chiarac99/2DShapeRenderingPantograph/force model/Hapkit_Pantograph_ForceFeedback_motor1_v1_slowOK.ino

//--------------------------------------------------------------------------
// ME327 Team 10 - Pantograph Haptic Shape Renderer
// Penetration depth + Force feedback function
//
// This file implements:
//   (1) A closed-loop shape (default: fat round-cornered star, 180 pts)
//       with a clearly marked slot for swapping in real Python-generated shapes
//   (2) Arc-length precomputation for texture rendering
//   (3) CCW winding check at startup (signed area via shoelace formula)
//   (4) Nearest-segment search + signed distance (penetration depth)
//   (5) Ray-casting inside/outside test
//   (6) Force feedback model with three regions on SIGNED penetration depth
//       (d > 0 = inside, d < 0 = outside):
//         d > 0:          linear wall spring + damping + (optional) texture
//         P_T < d <= 0:   dead zone, F = 0
//         d <= P_T:       exponential guidance pulling toward outline
//   (7) Two modes: MODE_CONTROL (no texture) and MODE_TEXTURED (sinusoidal)
//   (8) Forward kinematics (geometric, with corrected signs)
//   (9) Jacobian transpose (Cartesian force -> motor torques)
//   (10) PWM motor command output with direction control
//
// [TUNE WHEN HARDWARE READY] markers throughout the file flag values
// that need to be confirmed or re-calibrated once the pantograph is
// physically built.
//--------------------------------------------------------------------------

#include <math.h>
#include <avr/pgmspace.h>
#include <SoftwareSerial.h>

// ============================================================
// BOARD ROLE
// ============================================================
// Both Hapkit boards run identical firmware EXCEPT for this single line.
// Comment/uncomment to indicate which motor this board controls:
//
//   #define IS_MOTOR_1   <- this board drives motor 1 (theta_1 = own encoder)
//   (commented out)      <- this board drives motor 5 (theta_5 = own encoder)
//
// Both boards independently compute the full force model and both
// torques (tau1, tau5) via the Jacobian transpose. Each board then
// writes ONLY ITS OWN torque to its local motor:
//   IS_MOTOR_1 defined   -> writes tau1
//   IS_MOTOR_1 undefined -> writes tau5
//
// Hardware communication: the two boards exchange joint angles via a
// SoftwareSerial link on pins D9 (TX) and D10 (RX), keeping the hardware
// UART on D0/D1 free for USB Serial Monitor debugging. No host PC is
// needed in the control loop. Each board sends its own theta as
// "A<value>\n" and receives the partner's theta the same way.
//
// Wiring between boards (in addition to common GND):
//   Board 1 D9 (TX)  ->  Board 2 D10 (RX)
//   Board 1 D10 (RX) <-  Board 2 D9  (TX)
#define IS_MOTOR_1


// ============================================================
// PANTOGRAPH LINK LENGTHS  [meters]
// ============================================================
// Used by forward kinematics and Jacobian (stubs at the bottom of this
// file). Modify here when CAD is finalized. Convention follows Campion
// et al. 2005, with motor pivots coincident (a5 = 0) for wider workspace.
//
// Note: named LINK_A1..LINK_A5 (not A1..A5) because Arduino reserves the
// short A1..A5 names for analog pin aliases (PIN_A1, PIN_A2, ...).
//
//        P3 (pen tip)
//       /  \
//     a3    a2
//     /      \
//    P4      P2
//    |        |
//    a4       a1
//    |        |
//      P5/P1   <-- both motor pivots; a5 = 0 (coincident)
//
// [TUNE WHEN HARDWARE READY: set these to the actual CAD lengths]
const float LINK_A1 = 0.10f;    // proximal link, motor 1 side
const float LINK_A2 = 0.10f;    // distal link, motor 1 side (P2 -> P3)
const float LINK_A3 = 0.10f;    // distal link, motor 5 side (P4 -> P3)
const float LINK_A4 = 0.10f;    // proximal link, motor 5 side
const float LINK_A5 = 0.000f;    // distance between motor pivots (coincident)


// ============================================================
// HAPKIT HARDWARE PIN ASSIGNMENTS
// ============================================================
// From HapkitBoardPinMapping.pdf (v 11.14.2013):
//   D5  Motor 1 PWM
//   D6  Motor 2 PWM (unused in two-board pantograph; used in single-board)
//   D7  Motor 2 direction (unused in two-board)
//   D8  Motor 1 direction
//   D9  Grove connector output (used here as SoftwareSerial TX to partner)
//   D10 Grove connector output (used here as SoftwareSerial RX from partner)
//   A2  MR sensor (this board's encoder)
// [TUNE WHEN HARDWARE READY: if this is the "motor 5" board rather than
//  the "motor 1" board, change neither the pin numbers nor the variable
//  names -- just swap which torque the local motor receives in
//  sendMotorCommand below.]
const int sensorPosPin   = A2;     // MR sensor input
const int PWM_PIN_LOCAL  = 5;      // D5 PWM for this board's motor
const int DIR_PIN_LOCAL  = 8;      // D8 direction for this board's motor

// SoftwareSerial pins for the inter-board UART (D9 TX, D10 RX). The
// hardware UART (D0/D1) is reserved for USB Serial Monitor debugging.
const int LINK_TX_PIN    = 9;      // D9 -> partner's D10
const int LINK_RX_PIN    = 10;     // D10 <- partner's D9
SoftwareSerial linkSerial(LINK_RX_PIN, LINK_TX_PIN);  // (rx, tx)


// ============================================================
// CAPSTAN DRIVE TRANSMISSION  (per Hapkit board)
// ============================================================
// On the Hapkit, the motor pulley rotates the sector pulley via a
// capstan-drive cable, with a transmission ratio set by their radii.
// Tp = F * (r_handle * r_pulley) / r_sector             (A3 Hapkit, scalar)
// For the pantograph, the SAME capstan transmission converts motor torque
// to torque-at-the-proximal-link, but the link rotation directly drives
// the corresponding theta (no separate "handle" variable here; the link
// itself acts as the handle).
//
// Default values are the A3 Hapkit radii. Re-measure for the pantograph
// build if the capstan radii differ (e.g. if you change the drum or use
// a different sector size).
// [TUNE WHEN HARDWARE READY]
const float R_PULLEY  = 0.0045f;    // m, motor capstan/drum radius   (A3: 0.0045)
const float R_SECTOR  = 0.048f;     // m, sector pulley radius         (A3: 0.075)
// R_HANDLE was 0.087 m on the A3 Hapkit but it represents the distance
// from the sector axis to the user's handle. On the pantograph the user
// doesn't grip the sector directly -- they hold the pen tip P3 -- so
// R_HANDLE doesn't apply the same way. The Jacobian transpose already
// maps F at P3 to torque at each motor's sector, so we only need the
// capstan ratio (R_PULLEY / R_SECTOR) here.
//
// Capstan ratio for converting sector torque to motor torque:
//   tau_motor = tau_sector * (R_PULLEY / R_SECTOR)
const float CAPSTAN_RATIO = R_PULLEY / R_SECTOR;


// ============================================================
// TORQUE-TO-PWM CALIBRATION
// ============================================================
// Conversion formula from A3: duty = sqrt(|tau_motor| / TORQUE_TO_DUTY_K)
// The constant 0.0183 was calibrated for the single-Hapkit setup
// (relates motor-pulley torque to PWM duty cycle through the motor's
// torque constant + amplifier gain).
// [TUNE WHEN HARDWARE READY: re-measure for the pantograph motors if
//  they differ from the A3 Hapkit's, e.g. by applying a known voltage
//  and measuring the stall torque.]
const float TORQUE_TO_DUTY_K = 0.0183f;


// ============================================================
// ENCODER CALIBRATION  (from A3)
// ============================================================
// [TUNE WHEN HARDWARE READY: re-measure on each Hapkit board]
const float ENC_M    = -0.0221f;            // deg per encoder count (motor 1, R^2=0.997)
const float ENC_B    = 0.0f;             // deg offset; updatedPos=0 at 0deg by design
const float SECTOR_GEAR_REDUCTION = 1.0f;  // (motor angle) / (sector angle).
                                           // 1.0 if encoder directly measures
                                           // motor pulley; else the gear ratio.



// ============================================================
// CONDITION TOGGLE
// ============================================================
// Switch between control (no texture) and textured rendering.
// Later this can be set by a serial command from Processing so
// the database can log which condition each trial used.
enum RenderMode { MODE_CONTROL = 0, MODE_TEXTURED = 1 };
RenderMode renderMode = MODE_TEXTURED;   // change for testing


// ============================================================
// FORCE MODEL PARAMETERS (placeholders based on A3/A4 values)
// ============================================================
// Sign convention: penetration_depth d is SIGNED.
//   d > 0   -> user is INSIDE the shape (positive = penetrated)
//   d < 0   -> user is OUTSIDE the shape
//   |d|     -> perpendicular distance to the nearest segment of the outline
//
// Three regions on signed d:
//   d > 0:          F = -K_WALL * d        (linear wall, pushes outward)
//                                          (+ texture in textured mode)
//                                          (+ wall damping when moving in)
//   P_T < d <= 0:   F = 0                  (dead zone near the outline)
//   d <= P_T:       F = A_GUIDE * exp(-C_GUIDE * (d - P_T))
//                                          (guidance pulling toward shape;
//                                           peaks at A_GUIDE at d = P_T,
//                                           grows as d gets more negative)

// Inside-shape linear wall stiffness.
const float K_WALL = 2000.0f;       // N/m

// Wall damping (only active when user is moving INTO the wall, v_n > 0).
// Adds B_WALL * v_normal to the wall force. Improves stability (lets us
// run K_WALL higher than the undamped A2 bound would allow) and makes
// impacts feel more solid by dissipating kinetic energy on contact.
const float B_WALL = 15.0f;         // Ns/m

// Dead zone width (P_T is negative -- it's a depth on the outside).
const float P_T = -0.003f;          // m, 3 mm dead zone outside the outline

// Exponential guidance force parameters:
//   A_GUIDE       = force magnitude at d = P_T (peak at zone edge)
//   C_GUIDE       = decay rate (1/m); larger = sharper drop-off near P_T
//   F_GUIDE_MAX   = saturation ceiling for guidance force; once the exp
//                   exceeds this value, F is clamped to F_GUIDE_MAX
//                   so the motors never command more than they can deliver
const float A_GUIDE     = 0.5f;     // N, peak guidance force at d = P_T
const float C_GUIDE     = 200.0f;   // 1/m; exp doubles every ~3.5 mm further out
const float F_GUIDE_MAX = 2.0f;     // N, clamp ceiling (set to ~motor force limit)

// Texture parameters (for MODE_TEXTURED):
const float A_TEX = 0.30f;          // N, texture amplitude
const float LAMBDA_TEX = 0.0020f;   // m, spatial wavelength (2 mm bumps)


// ============================================================
// SHAPE DATA
// ============================================================
// Three closed-loop shapes derived from SVG outlines by the Python
// preprocessing script (preprocess_shapes.py). Each is 200 points,
// normalized so it fits in a ~7 cm bounding box centered at the
// origin, CCW winding. Coordinates are in meters.
//
// Switch between them at runtime by changing CURRENT_SHAPE, or by
// sending a single ASCII character over Serial: 'B' (bunny),
// 'H' (hammer), 'P' (pear).  Later this command will come from
// Processing when the user clicks "Next shape" in the UI.
//
// NOTE: Each shape array currently ends with a duplicate of the first
// point (a relic of the Python script's "close the curve" step). The
// findNearestSegment loop guards against the resulting zero-length
// segment, but consider trimming the duplicate (and dropping N to 199)
// in the next Python regen for cleanliness.

enum ShapeId { SHAPE_BUNNY = 0, SHAPE_HAMMER = 1, SHAPE_PEAR = 2 };
ShapeId currentShape = SHAPE_BUNNY;     // change here for testing

// All shapes happen to have the same point count for now (200), but the
// architecture allows different counts per shape if needed.
const int N_BUNNY  = 200;
const int N_HAMMER = 200;
const int N_PEAR   = 200;

// ----- bunny, 200 pts, CCW -----
const float shape_bunny[N_BUNNY][2] PROGMEM = {
    {  0.00328f,  0.03500f},
    {  0.00198f,  0.03445f},
    {  0.00007f,  0.03328f},
    { -0.00150f,  0.03201f},
    { -0.00281f,  0.03115f},
    { -0.00705f,  0.02830f},
    { -0.00908f,  0.02652f},
    { -0.01059f,  0.02515f},
    { -0.01081f,  0.02493f},
    { -0.01092f,  0.02487f},
    { -0.01101f,  0.02487f},
    { -0.01108f,  0.02487f},
    { -0.01114f,  0.02487f},
    { -0.01118f,  0.02489f},
    { -0.01122f,  0.02492f},
    { -0.01125f,  0.02496f},
    { -0.01129f,  0.02500f},
    { -0.01129f,  0.02504f},
    { -0.01123f,  0.02511f},
    { -0.01117f,  0.02531f},
    { -0.01087f,  0.02665f},
    { -0.01087f,  0.02781f},
    { -0.01117f,  0.02907f},
    { -0.01147f,  0.02955f},
    { -0.01210f,  0.03042f},
    { -0.01247f,  0.03064f},
    { -0.01395f,  0.03108f},
    { -0.01449f,  0.03113f},
    { -0.01558f,  0.03088f},
    { -0.01671f,  0.03036f},
    { -0.01714f,  0.02992f},
    { -0.01752f,  0.02924f},
    { -0.01847f,  0.02674f},
    { -0.01906f,  0.02462f},
    { -0.01966f,  0.02211f},
    { -0.01993f,  0.02162f},
    { -0.02006f,  0.02134f},
    { -0.02022f,  0.02119f},
    { -0.02046f,  0.02115f},
    { -0.02206f,  0.02115f},
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
};

// ----- hammer, 200 pts, CCW -----
const float shape_hammer[N_HAMMER][2] PROGMEM = {
    {  0.01861f, -0.01738f},
    {  0.01862f, -0.01740f},
    {  0.01863f, -0.01742f},
    {  0.01864f, -0.01745f},
    {  0.01867f, -0.01748f},
    {  0.01872f, -0.01751f},
    {  0.01886f, -0.01753f},
    {  0.02000f, -0.01752f},
    {  0.02049f, -0.01751f},
    {  0.02071f, -0.01746f},
    {  0.02116f, -0.01727f},
    {  0.02369f, -0.01616f},
    {  0.02512f, -0.01528f},
    {  0.02673f, -0.01401f},
    {  0.02831f, -0.01247f},
    {  0.02961f, -0.01089f},
    {  0.03057f, -0.00940f},
    {  0.03150f, -0.00754f},
    {  0.03217f, -0.00571f},
    {  0.03275f, -0.00326f},
    {  0.03315f, -0.00047f},
    {  0.03318f,  0.00067f},
    {  0.03312f,  0.00140f},
    {  0.03299f,  0.00199f},
    {  0.03278f,  0.00258f},
    {  0.03240f,  0.00334f},
    {  0.03171f,  0.00460f},
    {  0.03157f,  0.00493f},
    {  0.03152f,  0.00513f},
    {  0.03149f,  0.00551f},
    {  0.03150f,  0.00668f},
    {  0.03154f,  0.00701f},
    {  0.03162f,  0.00728f},
    {  0.03179f,  0.00768f},
    {  0.03194f,  0.00797f},
    {  0.03211f,  0.00820f},
    {  0.03234f,  0.00844f},
    {  0.03276f,  0.00878f},
    {  0.03384f,  0.00949f},
    {  0.03401f,  0.00964f},
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
};

// ----- pear, 200 pts, CCW -----
const float shape_pear[N_PEAR][2] PROGMEM = {
    { -0.00260f,  0.03430f},
    { -0.00341f,  0.03469f},
    { -0.00377f,  0.03482f},
    { -0.00411f,  0.03490f},
    { -0.00453f,  0.03496f},
    { -0.00528f,  0.03500f},
    { -0.01129f,  0.03475f},
    { -0.01401f,  0.03468f},
    { -0.01441f,  0.03464f},
    { -0.01462f,  0.03460f},
    { -0.01476f,  0.03455f},
    { -0.01485f,  0.03451f},
    { -0.01493f,  0.03448f},
    { -0.01499f,  0.03444f},
    { -0.01503f,  0.03440f},
    { -0.01507f,  0.03436f},
    { -0.01511f,  0.03432f},
    { -0.01514f,  0.03428f},
    { -0.01516f,  0.03423f},
    { -0.01519f,  0.03418f},
    { -0.01521f,  0.03412f},
    { -0.01522f,  0.03405f},
    { -0.01523f,  0.03397f},
    { -0.01523f,  0.03387f},
    { -0.01522f,  0.03373f},
    { -0.01519f,  0.03353f},
    { -0.01510f,  0.03319f},
    { -0.01481f,  0.03243f},
    { -0.01305f,  0.02866f},
    { -0.01240f,  0.02751f},
    { -0.01193f,  0.02685f},
    { -0.01127f,  0.02609f},
    { -0.01059f,  0.02542f},
    { -0.00997f,  0.02492f},
    { -0.00935f,  0.02450f},
    { -0.00871f,  0.02416f},
    { -0.00807f,  0.02389f},
    { -0.00744f,  0.02369f},
    { -0.00680f,  0.02355f},
    { -0.00617f,  0.02348f},
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
};

// Active shape: a pointer to the current PROGMEM array + its length.
// Shape data lives in flash (PROGMEM) to fit on the ATmega328's small
// RAM (only 2 KB; all three shapes together would be ~4.8 KB if in RAM).
// Access via shapeX(i) / shapeY(i) helpers below, NOT through direct
// indexing -- AVR flash and RAM are on separate buses.
const float (*shape)[2] = shape_bunny;
int N_POINTS = N_BUNNY;

// Read x or y of the i-th vertex of the active shape, from PROGMEM.
inline float shapeX(int i) {
  return pgm_read_float(&shape[i][0]);
}
inline float shapeY(int i) {
  return pgm_read_float(&shape[i][1]);
}



// ============================================================
// PRECOMPUTED TABLES
// ============================================================
// s_arc is sized to the maximum possible point count across all shapes,
// since the active shape can be swapped at runtime. The currently-active
// portion is the first N_POINTS entries.
#define MAX_POINTS 200
float s_arc[MAX_POINTS];
float perimeter = 0.0f;
float lambda_actual = LAMBDA_TEX;


// ============================================================
// VELOCITY TRACKING  (for wall damping)
// ============================================================
// Position from the previous loop, used to compute filtered velocity.
// Same finite-difference + IIR filter pattern as A3/A4.
float xh_prev = 0.0f, yh_prev = 0.0f;
float vx_filt = 0.0f, vy_filt = 0.0f;
const float DT_LOOP = 0.001f;       // s, nominal loop period (1 kHz)


// ============================================================
// ENCODER STATE  (mirrors A3 template)
// ============================================================
// Declared up here (above loop) so the telemetry print can reference
// updatedPos directly without needing extern forward declarations.
int rawPos = 0, lastRawPos = 0, lastLastRawPos = 0;
int rawDiff = 0, lastRawDiff = 0, rawOffset = 0, lastRawOffset = 0;
int flipNumber = 0;
int tempOffset = 0;
bool flipped = false;
const int flipThresh = 700;
int updatedPos = 0;

// Partner-board angle, received over serial.
// [TUNE WHEN HARDWARE READY: pick a sensible startup angle inside the
//  valid workspace, e.g. PI/2 for the elbow-up configuration.]
float theta_partner_rad = PI / 2.0f;

// Last computed pen-tip position (persists between loops when getPenTip
// has bad/no data this iteration).
float xh_persist = 0.0f, yh_persist = 0.0f;


// ============================================================
// FORWARD DECLARATIONS
// ============================================================
void   getPenTipPosition(float &x, float &y, float theta_self);
int    findNearestSegment(float x, float y, float &dist, float &nx, float &ny,
                          float &t_frac);
bool   isInsidePolygon(float x, float y);
void   computeForce(float x, float y, float &Fx, float &Fy);
void   computeMotorTorques(float Fx, float Fy, float &tau1, float &tau5, float theta_self);
void   sendMotorCommand(float tau1, float tau5, float theta_self);
void   precomputeArcLength();
float  signedPolygonArea();
void   checkWinding();
void   setShape(ShapeId s);
void   handleSerialCommands();


// ============================================================
// SETUP
// ============================================================
// PWM frequency divisor helper (copied from A3 template -- DO NOT EDIT).
// Increases PWM frequency on the motor pins to keep motor noise inaudible
// and force-response smooth.
void setPwmFrequency(int pin, int divisor) {
  byte mode;
  if(pin == 5 || pin == 6 || pin == 9 || pin == 10) {
    switch(divisor) {
      case 1: mode = 0x01; break;
      case 8: mode = 0x02; break;
      case 64: mode = 0x03; break;
      case 256: mode = 0x04; break;
      case 1024: mode = 0x05; break;
      default: return;
    }
    if(pin == 5 || pin == 6) {
      TCCR0B = TCCR0B & 0b11111000 | mode;
    } else {
      TCCR1B = TCCR1B & 0b11111000 | mode;
    }
  } else if(pin == 3 || pin == 11) {
    switch(divisor) {
      case 1: mode = 0x01; break;
      case 8: mode = 0x02; break;
      case 32: mode = 0x03; break;
      case 64: mode = 0x04; break;
      case 128: mode = 0x05; break;
      case 256: mode = 0x06; break;
      case 1024: mode = 0x07; break;
      default: return;
    }
    TCCR2B = TCCR2B & 0b11111000 | mode;
  }
}

void setup() {
  Serial.begin(115200);      // USB serial for debugging + user commands
  linkSerial.begin(19200);   // SoftwareSerial inter-board link (D9/D10)
                             // 19200 is the highest baud SoftwareSerial
                             // handles reliably on a 16 MHz AVR.
  linkSerial.setTimeout(10); // cap parseFloat blocking at 10 ms

  // Configure motor PWM at high frequency (matches A3 template).
  setPwmFrequency(PWM_PIN_LOCAL, 1);

  // Configure motor and encoder pins.
  pinMode(sensorPosPin, INPUT);
  pinMode(PWM_PIN_LOCAL, OUTPUT);
  pinMode(DIR_PIN_LOCAL, OUTPUT);
  analogWrite(PWM_PIN_LOCAL, 0);          // motor off at startup
  digitalWrite(DIR_PIN_LOCAL, LOW);

  setShape(currentShape);  // initializes shape pointer, arc-length table, prints CCW check
}


// ============================================================
// MAIN LOOP
// ============================================================
void loop() {
  handleSerialCommands();

  // Sample encoder ONCE per loop. Pass cached value to all functions that
  // need it (rather than re-reading inside each function), since re-reads
  // were confusing the flip-detector during fast motion.
  float theta_self_cached = readThisBoardTheta();

  float xh, yh;
  getPenTipPosition(xh, yh, theta_self_cached);

  float vx = (xh - xh_prev) / DT_LOOP;
  float vy = (yh - yh_prev) / DT_LOOP;
  vx_filt = 0.9f * vx + 0.1f * vx_filt;
  vy_filt = 0.9f * vy + 0.1f * vy_filt;
  xh_prev = xh;
  yh_prev = yh;

  float Fx, Fy;
  computeForce(xh, yh, Fx, Fy);

  // ---- SAFETY: force motors OFF for calibration test ----
  Fx = 0.0f;
  Fy = 0.0f;

  float tau1, tau5;
  computeMotorTorques(Fx, Fy, tau1, tau5, theta_self_cached);

  sendMotorCommand(tau1, tau5, theta_self_cached);

  // Telemetry: print updatedPos every 50 loops so you can watch it sweep
  static int printCounter = 0;
  if (++printCounter >= 50) {
    float ts_deg = ENC_M * updatedPos + ENC_B;
    Serial.print("updatedPos=");  Serial.print(updatedPos);
    Serial.print("  theta_deg=");  Serial.print(ts_deg, 1);
    Serial.print("  partner_rad=");  Serial.print(theta_partner_rad, 3);
    Serial.print("  xh,yh=");     Serial.print(xh, 4);
    Serial.print(",");            Serial.print(yh, 4);
    Serial.println();
    printCounter = 0;
  }
}


// ============================================================
// ENCODER READING + FORWARD KINEMATICS
// ============================================================
// This board reads ONE encoder (its own motor's MR sensor on pin A2) and
// computes θ for that joint. The OTHER joint angle (θ for the other motor)
// must arrive over serial from the partner Hapkit board, or via a host
// (Processing) that polls both boards.
//
// Below, theta1_rad is the angle this board's motor; theta5_rad is the
// other board's motor (received over serial). If this is the "motor 5"
// board, swap the assignments in computeFwdKin() accordingly.
//
// Forward kinematics follows the geometric approach from the wiki:
//   1. P2 = (LINK_A1*cos(theta1), LINK_A1*sin(theta1))
//   2. P4 = (-LINK_A5 + LINK_A4*cos(theta5), LINK_A4*sin(theta5))
//   3. |P2-Pn| = (LINK_A2^2 - LINK_A3^2 + |P4-P2|^2) / (2|P4-P2|)
//   4. Ph = P2 + |P2-Pn|/|P2-P4| * (P4-P2)
//   5. |P3-Ph| = sqrt(LINK_A2^2 - |P2-Pn|^2)
//   6. P3 = Ph + |P3-Ph|/|P4-P2| * (y4-y2, -(x4-x2))    [elbow-up sign]

// --------- Read this board's encoder (returns theta in radians) ---------
// NOTE: this is called multiple times per loop (in getPenTipPosition,
// computeMotorTorques, and sendMotorCommand's theta broadcast). The flip
// state machine assumes consecutive calls correspond to consecutive
// physical timesteps; if you observe flip-counting issues, refactor to
// sample once per loop and cache the result.
float readThisBoardTheta() {
  rawPos = analogRead(sensorPosPin);
  rawDiff = rawPos - lastRawPos;
  lastRawDiff = rawPos - lastLastRawPos;
  rawOffset = abs(rawDiff);
  lastRawOffset = abs(lastRawDiff);
  lastLastRawPos = lastRawPos;
  lastRawPos = rawPos;

  if ((lastRawOffset > flipThresh) && (!flipped)) {
    if (lastRawDiff > 0) flipNumber--; else flipNumber++;
    if (rawOffset > flipThresh) {
      updatedPos = rawPos + flipNumber * rawOffset;
      tempOffset = rawOffset;
    } else {
      updatedPos = rawPos + flipNumber * lastRawOffset;
      tempOffset = lastRawOffset;
    }
    flipped = true;
  } else {
    updatedPos = rawPos + flipNumber * tempOffset;
    flipped = false;
  }

  float ts_deg = ENC_M * updatedPos + ENC_B;            // sector angle (deg)
  float theta_motor_deg = ts_deg * SECTOR_GEAR_REDUCTION;
  float theta_motor_rad = theta_motor_deg * (PI / 180.0f);
  return theta_motor_rad;
}

// --------- Geometric forward kinematics ---------
// Returns true if a valid configuration was found, false otherwise (e.g.
// linkage is in a singular pose).
bool computeFwdKin(float theta1, float theta5, float &x3, float &y3) {
  static int dbg = 0;
  bool doPrint = (++dbg >= 500);
  if (doPrint) dbg = 0;
  
  float x2 = LINK_A1 * cosf(theta1);
  float y2 = LINK_A1 * sinf(theta1);
  float x4 = -LINK_A5 + LINK_A4 * cosf(theta5);
  float y4 = LINK_A4 * sinf(theta5);

  float dx = x4 - x2;
  float dy = y4 - y2;
  float dP2P4 = sqrtf(dx*dx + dy*dy);
  
  if (doPrint) {
    Serial.print("  FK: t1=");Serial.print(theta1,3);
    Serial.print(" t5=");Serial.print(theta5,3);
    Serial.print(" P2=("); Serial.print(x2,3); Serial.print(",");Serial.print(y2,3);
    Serial.print(") P4=("); Serial.print(x4,3); Serial.print(",");Serial.print(y4,3);
    Serial.print(") dP2P4="); Serial.print(dP2P4,4);
    Serial.println();
  }
  
  if (dP2P4 < 1e-6f) { if(doPrint) Serial.println("  -> ret false (singular)"); return false; }

  float dP2Ph = (LINK_A2*LINK_A2 - LINK_A3*LINK_A3 + dP2P4*dP2P4) / (2.0f * dP2P4);
  float h2 = LINK_A2*LINK_A2 - dP2Ph*dP2Ph;
  
  if (doPrint) {
    Serial.print("  dP2Ph="); Serial.print(dP2Ph,4);
    Serial.print(" h2="); Serial.print(h2,6);
    Serial.println();
  }
  
  if (h2 < 0.0f) { if(doPrint) Serial.println("  -> ret false (h2 negative)"); return false; }
  float dP3Ph = sqrtf(h2);

  float xh_pt = x2 + (dP2Ph / dP2P4) * dx;
  float yh_pt = y2 + (dP2Ph / dP2P4) * dy;

  x3 = xh_pt + (dP3Ph / dP2P4) * dy;
  y3 = yh_pt - (dP3Ph / dP2P4) * dx;
  
  if (doPrint) {
    Serial.print("  Ph=("); Serial.print(xh_pt,3); Serial.print(",");Serial.print(yh_pt,3);
    Serial.print(") P3=("); Serial.print(x3,3); Serial.print(",");Serial.print(y3,3);
    Serial.println(") -> ret true");
  }
  return true;
}

// --------- Public function the main loop calls ---------
void getPenTipPosition(float &x, float &y, float theta_self) {
  // theta_self is passed in (cached from loop()) instead of re-reading
  // the encoder, which was triggering spurious flip counts during fast motion.

  // Assign theta1 and theta5 based on which board this is.
#ifdef IS_MOTOR_1
  float theta1 = theta_self;
  float theta5 = theta_partner_rad;
#else
  float theta1 = theta_partner_rad;
  float theta5 = theta_self;
#endif

  float x3, y3;
  if (computeFwdKin(theta1, theta5, x3, y3)) {
    xh_persist = x3;
    yh_persist = y3;
  }
  // If computeFwdKin failed (singular/unreachable), reuse last good value.
  x = xh_persist;
  y = yh_persist;
}


// ============================================================
// PRECOMPUTE ARC-LENGTH TABLE
// ============================================================
// Walks the (closed) shape once to fill s_arc[i] and total perimeter.
// Snaps lambda_actual to perimeter/round(perimeter/LAMBDA_TEX) so the
// sine wave closes cleanly at the seam where shape[N-1] -> shape[0].
void precomputeArcLength() {
  s_arc[0] = 0.0f;
  for (int i = 1; i < N_POINTS; i++) {
    float dx = shapeX(i) - shapeX(i-1);
    float dy = shapeY(i) - shapeY(i-1);
    s_arc[i] = s_arc[i-1] + sqrtf(dx*dx + dy*dy);
  }
  float dx_close = shapeX(0) - shapeX(N_POINTS-1);
  float dy_close = shapeY(0) - shapeY(N_POINTS-1);
  perimeter = s_arc[N_POINTS-1] + sqrtf(dx_close*dx_close + dy_close*dy_close);

  int n_cycles = (int)roundf(perimeter / LAMBDA_TEX);
  if (n_cycles < 1) n_cycles = 1;
  lambda_actual = perimeter / (float)n_cycles;
}


// ============================================================
// SIGNED POLYGON AREA  (shoelace formula)
// ============================================================
// Positive area means CCW winding (interior on the left as you walk
// the array forward). Negative means CW. Used to verify the shape
// array has the orientation the rest of the code assumes.
float signedPolygonArea() {
  float area = 0.0f;
  for (int i = 0; i < N_POINTS; i++) {
    int j = (i + 1) % N_POINTS;
    area += shapeX(i) * shapeY(j) - shapeX(j) * shapeY(i);
  }
  return 0.5f * area;
}


// ============================================================
// WINDING CHECK  (warn over serial if CW)
// ============================================================
void checkWinding() {
  float area = signedPolygonArea();
  if (area < 0.0f) {
    Serial.println("!!! WARNING: shape array is CW. Force normals will point");
    Serial.println("!!! INWARD. Reverse the array order in Python (or here)");
    Serial.println("!!! before testing.");
  } else {
    Serial.print("Shape OK (CCW), area = ");
    Serial.print(area, 6);
    Serial.println(" m^2");
  }
}


// ============================================================
// SET SHAPE  (runtime switcher)
// ============================================================
// Swaps the active shape pointer + length, then rebuilds the arc-length
// table and verifies winding. Called once in setup() and again whenever
// a shape-switch command arrives over serial.
void setShape(ShapeId s) {
  currentShape = s;
  switch (s) {
    case SHAPE_BUNNY:
      shape = shape_bunny;
      N_POINTS = N_BUNNY;
      Serial.println("Active shape: BUNNY");
      break;
    case SHAPE_HAMMER:
      shape = shape_hammer;
      N_POINTS = N_HAMMER;
      Serial.println("Active shape: HAMMER");
      break;
    case SHAPE_PEAR:
      shape = shape_pear;
      N_POINTS = N_PEAR;
      Serial.println("Active shape: PEAR");
      break;
  }
  precomputeArcLength();
  checkWinding();
}


// ============================================================
// HANDLE SERIAL COMMANDS  (called once per loop)
// ============================================================
// Two serial streams are processed:
//
// 1. USB Serial (hardware UART, D0/D1):
//    Single-character commands from the Serial Monitor or host PC:
//      'B' / 'b' -> switch to bunny
//      'H' / 'h' -> switch to hammer
//      'P' / 'p' -> switch to pear
//      'C' / 'c' -> control mode (no texture)
//      'T' / 't' -> textured mode
//
// 2. linkSerial (SoftwareSerial, D9 TX / D10 RX):
//    Multi-character commands from the partner board:
//      "A<float>\n" -> set theta_partner_rad (joint angle from partner)
//
// Whitespace and unrecognized bytes are silently consumed.
void handleSerialCommands() {
  // ----- USB Serial: user/host commands -----
  while (Serial.available()) {
    char c = (char)Serial.read();
    switch (c) {
      case 'B': case 'b': setShape(SHAPE_BUNNY);  break;
      case 'H': case 'h': setShape(SHAPE_HAMMER); break;
      case 'P': case 'p': setShape(SHAPE_PEAR);   break;
      case 'C': case 'c':
        renderMode = MODE_CONTROL;
        Serial.println("Mode: CONTROL");
        break;
      case 'T': case 't':
        renderMode = MODE_TEXTURED;
        Serial.println("Mode: TEXTURED");
        break;
      default:
        break;
    }
  }

  // ----- linkSerial: inter-board partner theta -----
  while (linkSerial.available()) {
    char c = (char)linkSerial.read();
    if (c == 'A') {
      float val = linkSerial.parseFloat();
      theta_partner_rad = val;
      // Consume the trailing newline if present
      while (linkSerial.available() &&
             (linkSerial.peek() == '\n' || linkSerial.peek() == '\r')) {
        linkSerial.read();
      }
    }
    // Anything else: ignore.
  }
}


// ============================================================
// NEAREST SEGMENT SEARCH
// ============================================================
// For each segment (shape[i], shape[i+1])  (wrapping at N-1 -> 0),
// computes the perpendicular distance from (x,y) to that segment,
// the segment's outward unit normal (assuming CCW polygon), and the
// fractional position t in [0,1] along the segment.
//
// Outward normal: for tangent (tx,ty), outward direction is (-ty, tx)
// when the polygon is CCW.
//
// IMPORTANT: skips zero-length segments. Without this guard, a degenerate
// segment (e.g. the duplicate first/last point in the closed shape array)
// produces seg_len2 = 0, then t = something/0 = Inf/NaN. AVR's software
// FP library handles NaN arithmetic ~30-100x slower than normal floats,
// which dragged the loop from ~5 ms to ~6 seconds before we caught it.
int findNearestSegment(float x, float y, float &dist, float &nx, float &ny,
                       float &t_frac) {
  int best_i = 0;
  float best_dist = 1.0e9f;
  float best_nx = 0.0f, best_ny = 0.0f;
  float best_t = 0.0f;

  for (int i = 0; i < N_POINTS; i++) {
    int j = (i + 1) % N_POINTS;

    float ax = shapeX(i), ay = shapeY(i);
    float bx = shapeX(j), by = shapeY(j);
    float tx = bx - ax;
    float ty = by - ay;
    float seg_len2 = tx*tx + ty*ty;

    // Skip degenerate (zero-length) segments to avoid divide-by-zero NaN.
    if (seg_len2 < 1e-12f) continue;

    float t = ((x - ax)*tx + (y - ay)*ty) / seg_len2;
    if (t < 0.0f) t = 0.0f;
    if (t > 1.0f) t = 1.0f;

    float px = ax + t*tx;
    float py = ay + t*ty;
    float ddx = x - px;
    float ddy = y - py;
    float d = sqrtf(ddx*ddx + ddy*ddy);

    if (d < best_dist) {
      best_dist = d;
      best_i = i;
      best_t = t;
      float seg_len = sqrtf(seg_len2);
      // Outward normal for a CCW polygon in math (y-up) coords:
      // rotate tangent -90 deg, i.e. (tx, ty) -> (ty, -tx).
      best_nx =  ty / seg_len;
      best_ny = -tx / seg_len;
    }
  }

  dist = best_dist;
  nx = best_nx;
  ny = best_ny;
  t_frac = best_t;
  return best_i;
}


// ============================================================
// INSIDE/OUTSIDE TEST  (ray casting)
// ============================================================
bool isInsidePolygon(float x, float y) {
  bool inside = false;
  for (int i = 0, j = N_POINTS - 1; i < N_POINTS; j = i++) {
    float xi = shapeX(i), yi = shapeY(i);
    float xj = shapeX(j), yj = shapeY(j);

    bool intersect = ((yi > y) != (yj > y)) &&
                     (x < (xj - xi) * (y - yi) / (yj - yi) + xi);
    if (intersect) inside = !inside;
  }
  return inside;
}


// ============================================================
// FORCE FEEDBACK MODEL
// ============================================================
// Uses SIGNED penetration depth (positive = inside, negative = outside).
//
// Three regions:
//   d > 0:         F_wall = -K_WALL * d * n_outward          (linear spring)
//                  + B_WALL * v_normal * (-n_outward)        (damping, only
//                                                              when moving in)
//                  + texture (textured mode only)
//   P_T < d <= 0:  F = 0                                     (dead zone)
//   d <= P_T:      F = A_GUIDE * exp(-C_GUIDE * (d - P_T))
//                       * (-n_outward)                       (pulls toward shape)
//
// Note: n_outward is the unit outward normal of the nearest segment.
// "Pushing the user outward from inside" = force along +n_outward,
// "Pulling the user inward from outside" = force along -n_outward.
//
// The form -K_WALL*d (with d > 0 inside) produces a magnitude K_WALL*|d|
// in the outward direction, consistent with the original Chiara diagram.
void computeForce(float x, float y, float &Fx, float &Fy) {
  // Find nearest segment and unsigned perpendicular distance.
  float unsigned_d, nx, ny, t_frac;
  int seg_i = findNearestSegment(x, y, unsigned_d, nx, ny, t_frac);

  // Convert to SIGNED penetration depth: positive inside, negative outside.
  bool inside = isInsidePolygon(x, y);
  float d = inside ? unsigned_d : -unsigned_d;

  // Velocity in the inward direction (positive = moving deeper into shape).
  // n_outward points outward, so inward velocity = -(v . n_outward).
  float v_inward = -(vx_filt * nx + vy_filt * ny);

  Fx = 0.0f;
  Fy = 0.0f;

  if (d > 0.0f) {
    // ---------- INSIDE the shape: linear wall spring (+ damping + texture)
    float F_wall_mag = K_WALL * d;  // magnitude in the outward-normal direction

    // Wall damping: opposes motion only when moving INTO the wall.
    // Avoids "sticky pull-out" when user retracts.
    if (v_inward > 0.0f) {
      F_wall_mag += B_WALL * v_inward;
    }

    Fx = F_wall_mag * nx;
    Fy = F_wall_mag * ny;

    // Texture force (textured condition only):
    if (renderMode == MODE_TEXTURED) {
      int next_i = (seg_i + 1) % N_POINTS;
      float seg_len = (next_i == 0)
                      ? (perimeter - s_arc[seg_i])
                      : (s_arc[next_i] - s_arc[seg_i]);
      float s = s_arc[seg_i] + t_frac * seg_len;

      float F_tex = A_TEX * sinf(2.0f * (float)PI * s / lambda_actual);
      Fx += F_tex * nx;
      Fy += F_tex * ny;
    }

  } else if (d > P_T) {
    // ---------- DEAD ZONE: no force, user can move freely near the outline
    Fx = 0.0f;
    Fy = 0.0f;

  } else {
    // ---------- FAR OUTSIDE: exponential guidance pulling toward the shape
    // F = A_GUIDE * exp(-C_GUIDE * (d - P_T))
    //   At d = P_T:   F = A_GUIDE  (peak guidance at dead-zone edge)
    //   At d < P_T:   F grows exponentially as user goes further out
    //   Clamped at F_GUIDE_MAX so the motors never have to deliver more
    //   force than they can handle.
    float F_guide = A_GUIDE * expf(-C_GUIDE * (d - P_T));
    if (F_guide > F_GUIDE_MAX) F_guide = F_GUIDE_MAX;
    // Sign flip: pull INWARD, opposite to outward normal.
    Fx = -F_guide * nx;
    Fy = -F_guide * ny;
  }
}


// ============================================================
// JACOBIAN TRANSPOSE  (Cartesian force -> motor torques)
// ============================================================
// Implements tau = J^T * F where J is the 2x2 Jacobian of the forward
// kinematics map. Follows the chain-rule expressions in Campion et al.
// 2005 (Pantograph Mk-II) with the corrected signs on the leaf partials
// of P2 and P4 (see the wiki Differential Kinematics section -- the
// paper's Eqs. (14)-(15) are missing negative signs on dx2/dt1 and
// dx4/dt5).
//
// Conventions:
//   theta1 = this board's motor angle (or whichever is "motor 1")
//   theta5 = partner board's motor angle
//   theta1 and theta5 are in RADIANS.
//
// Intermediate quantities (matching Campion's notation):
//   d = |P2 - P4|
//   b = |P2 - Ph|
//   h = |P3 - Ph|
//
// Indices throughout: subscript "1" = partial wrt theta1, "5" = wrt theta5.
// For brevity we compute the 8 entries we need: dx2/dt1, dy2/dt1, dx4/dt5,
// dy4/dt5, then chain through d, b, Ph, h, to x3, y3.
//
// The four partials d_i x3, d_i y3 (i in {1,5}) form the 2x2 J. J^T * F
// = [d1x3*Fx + d1y3*Fy ; d5x3*Fx + d5y3*Fy] = (tau1, tau5).
void computeMotorTorques(float Fx, float Fy, float &tau1, float &tau5, float theta_self) {
  // theta_self is passed in (cached from loop()) instead of re-reading
  // the encoder, which was triggering spurious flip counts.
#ifdef IS_MOTOR_1
  float theta1 = theta_self;
  float theta5 = theta_partner_rad;
#else
  float theta1 = theta_partner_rad;
  float theta5 = theta_self;
#endif

  // Elbow positions
  float x2 = LINK_A1 * cosf(theta1);
  float y2 = LINK_A1 * sinf(theta1);
  float x4 = -LINK_A5 + LINK_A4 * cosf(theta5);
  float y4 = LINK_A4 * sinf(theta5);

  float dx = x4 - x2;
  float dy = y4 - y2;
  float d  = sqrtf(dx*dx + dy*dy);
  if (d < 1e-6f) { tau1 = 0; tau5 = 0; return; }

  // b = |P2 - Ph|;  h = |P3 - Ph|
  float b  = (LINK_A2*LINK_A2 - LINK_A3*LINK_A3 + d*d) / (2.0f * d);
  float h2 = LINK_A2*LINK_A2 - b*b;
  if (h2 < 0.0f) { tau1 = 0; tau5 = 0; return; }
  float h  = sqrtf(h2);

  // ---------------------------------------------------------
  // Leaf partials (CORRECTED -- Campion paper has wrong signs
  // on the x-components of these two lines)
  // ---------------------------------------------------------
  float d1x2 = -LINK_A1 * sinf(theta1);   // partial of x2 wrt theta1
  float d1y2 =  LINK_A1 * cosf(theta1);
  float d5x4 = -LINK_A4 * sinf(theta5);   // partial of x4 wrt theta5
  float d5y4 =  LINK_A4 * cosf(theta5);

  // The "other-index" partials are zero (e.g. P2 doesn't depend on theta5):
  // d5x2 = d5y2 = d1x4 = d1y4 = 0
  // (no variables, just substituted as 0 below)

  // ---------------------------------------------------------
  // Chain rule, for index i = 1 then i = 5.
  // ---------------------------------------------------------
  // We compute two columns of the Jacobian: [d1x3, d1y3] and [d5x3, d5y3].
  float d1x3, d1y3, d5x3, d5y3;

  for (int pass = 0; pass < 2; pass++) {
    // i = 1 on pass 0, i = 5 on pass 1
    float dix2, diy2, dix4, diy4;
    if (pass == 0) {
      dix2 = d1x2; diy2 = d1y2;
      dix4 = 0.0f; diy4 = 0.0f;
    } else {
      dix2 = 0.0f; diy2 = 0.0f;
      dix4 = d5x4; diy4 = d5y4;
    }

    // d_i d  = ((x4-x2)*(dix4 - dix2) + (y4-y2)*(diy4 - diy2)) / d
    float did = ((x4 - x2)*(dix4 - dix2) + (y4 - y2)*(diy4 - diy2)) / d;

    // d_i b = d_i d - d_i d * (LINK_A2^2 - LINK_A3^2 + d^2) / (2 d^2)
    float dib = did - did * (LINK_A2*LINK_A2 - LINK_A3*LINK_A3 + d*d) / (2.0f * d*d);

    // d_i h = -b/h * d_i b
    float dih = -b * dib / h;

    // d_i yh = d_i y2 + ((dib*d - did*b)/d^2)(y4-y2) + (b/d)(diy4 - diy2)
    float diyh = diy2 + ((dib*d - did*b) / (d*d)) * (y4 - y2)
                 + (b/d) * (diy4 - diy2);

    // d_i xh = d_i x2 + ((dib*d - did*b)/d^2)(x4-x2) + (b/d)(dix4 - dix2)
    float dixh = dix2 + ((dib*d - did*b) / (d*d)) * (x4 - x2)
                 + (b/d) * (dix4 - dix2);

    // d_i y3 = d_i yh - (h/d)(dix4 - dix2) - ((dih*d - did*h)/d^2)(x4-x2)
    float diy3 = diyh - (h/d)*(dix4 - dix2)
                 - ((dih*d - did*h)/(d*d))*(x4 - x2);

    // d_i x3 = d_i xh + (h/d)(diy4 - diy2) + ((dih*d - did*h)/d^2)(y4-y2)
    float dix3 = dixh + (h/d)*(diy4 - diy2)
                 + ((dih*d - did*h)/(d*d))*(y4 - y2);

    if (pass == 0) { d1x3 = dix3; d1y3 = diy3; }
    else           { d5x3 = dix3; d5y3 = diy3; }
  }

  // ---------------------------------------------------------
  // tau = J^T * F
  //   tau1 = d_x3/d_t1 * Fx + d_y3/d_t1 * Fy
  //   tau5 = d_x3/d_t5 * Fx + d_y3/d_t5 * Fy
  // ---------------------------------------------------------
  tau1 = d1x3 * Fx + d1y3 * Fy;
  tau5 = d5x3 * Fx + d5y3 * Fy;
}


// ============================================================
// MOTOR COMMAND OUTPUT
// ============================================================
// Pin numbers, calibration constant, and motor-direction polarity were
// declared at the top of the file. Modify there.

// Write one motor (torque -> duty cycle + direction).
// Input `tau` is the torque at the sector pulley (which the Jacobian
// gives us). We convert to motor-pulley torque via the capstan ratio
// before mapping to PWM, since the PWM-vs-torque relation was calibrated
// at the motor pulley in A3.
void writeMotor(int pwmPin, int dirPin, float tau_sector) {
  float tau_motor = tau_sector * CAPSTAN_RATIO;

  // Direction: positive torque = HIGH, negative = LOW (A3 convention;
  // may need to be inverted depending on motor wiring polarity).
  // [TUNE WHEN HARDWARE READY: flip HIGH/LOW if motor pushes the wrong way]
  digitalWrite(dirPin, (tau_motor >= 0.0f) ? HIGH : LOW);

  float duty = sqrtf(fabsf(tau_motor) / TORQUE_TO_DUTY_K);
  if (duty > 1.0f) duty = 1.0f;
  if (duty < 0.0f) duty = 0.0f;
  int outVal = (int)(duty * 255.0f);
  analogWrite(pwmPin, outVal);
}

void sendMotorCommand(float tau1, float tau5, float theta_self) {
  // Each board writes ITS OWN motor only. The other board independently
  // computes the same torque values and writes its own motor.
#ifdef IS_MOTOR_1
  writeMotor(PWM_PIN_LOCAL, DIR_PIN_LOCAL, tau1);
#else
  writeMotor(PWM_PIN_LOCAL, DIR_PIN_LOCAL, tau5);
#endif

  // Broadcast OUR theta to the partner board over the inter-board UART.
  // Protocol: "A<value>\n" with value in radians. Rate-limit to avoid
  // saturating the SoftwareSerial bandwidth (it's ~9600-19200 baud
  // reliable, much slower than the hardware UART).
  static int thetaCounter = 0;
  if (++thetaCounter >= 20) {
    linkSerial.print("A");
    linkSerial.println(theta_self, 3);    // use cached value, no encoder re-read
    thetaCounter = 0;
  }
}
